osmonduu/Shooter-Controller-System/Docs/schematics/guncontroller.kicad_sch

## KiCad design Docs/schematics/guncontroller.kicad_sch (2025-05-13)

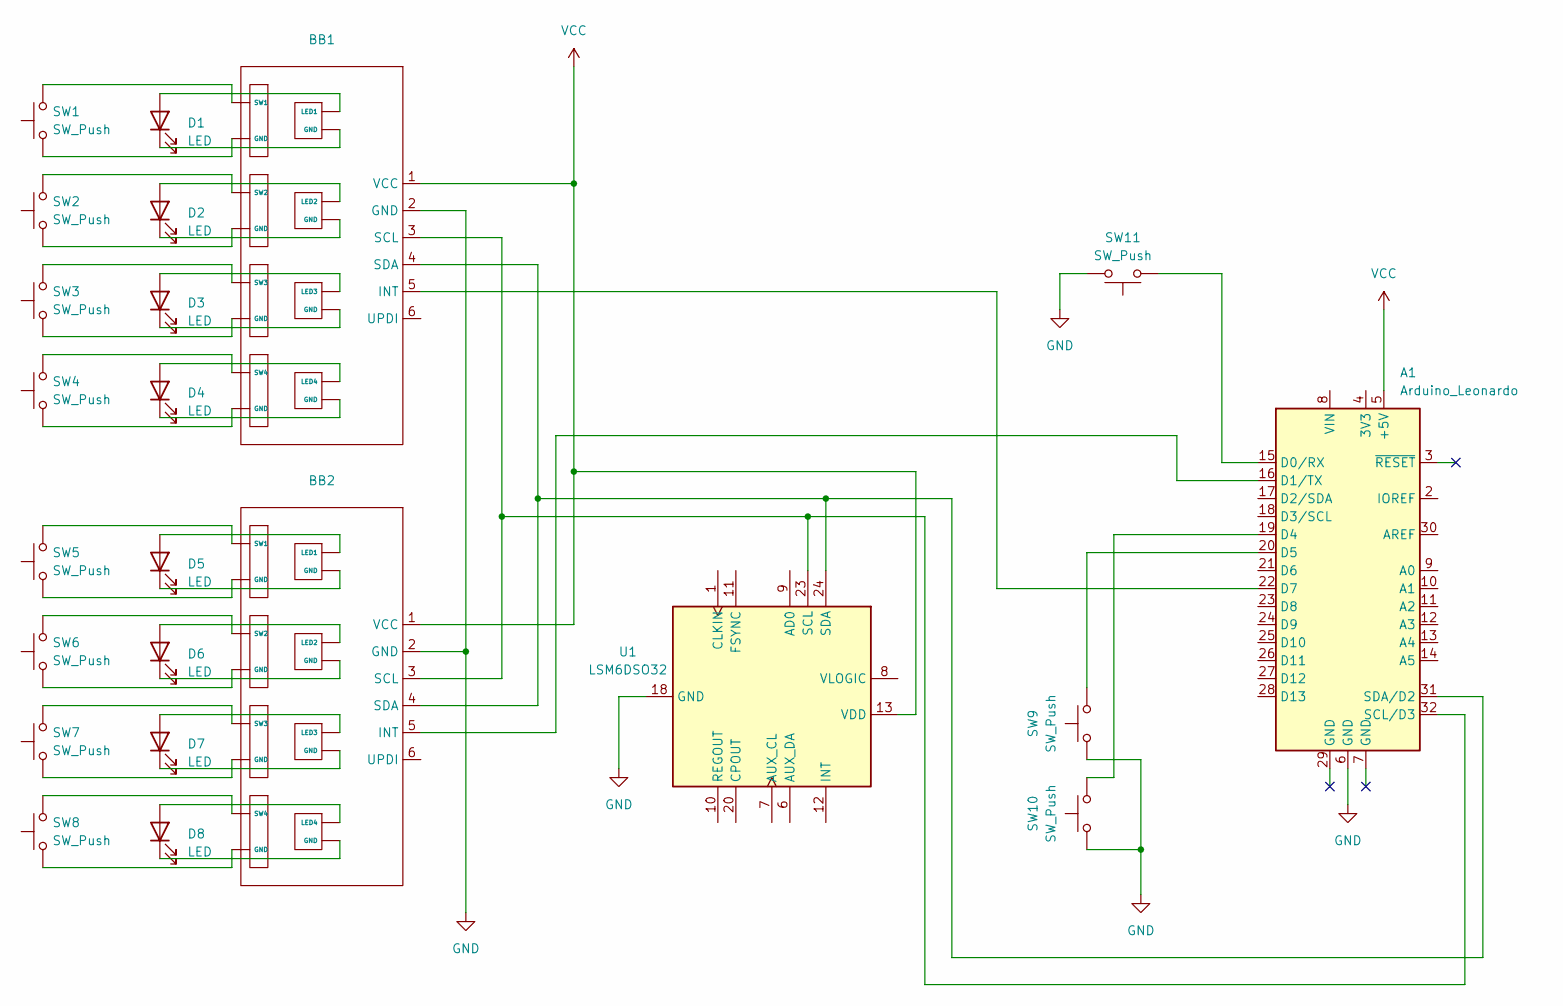
[picture p14: schematic guncontroller.kicad_sch]

Parts:
A1: Arduino_Leonardo; Arduino_UNO_R3
BB1, BB2: (no value)
D1, D2, D3, D4, D5, D6, D7, D8: LED
SW1, SW2, SW3, SW4, SW5, SW6, SW7, SW8, SW9, SW10, SW11: SW_Push
U1: LSM6DSO32; InvenSense_QFN-24_4x4mm_P0.5mm

Connections:
GND: A1.6 (GND), BB1.2 (GND), BB2.2 (GND), SW9.1, SW10.1, SW11.2, U1.18 (GND)
unnamed: A1.15 (D0/RX), SW11.1
unnamed: A1.16 (D1/TX), BB2.5 (INT)
unnamed: A1.19 (D4), SW10.2
unnamed: A1.20 (D5), SW9.2
unnamed: A1.22 (D7), BB1.5 (INT)
unnamed: A1.31 (SDA/D2), BB1.4 (SDA), BB2.4 (SDA), U1.24 (SDA)
unnamed: A1.32 (SCL/D3), BB1.3 (SCL), BB2.3 (SCL), U1.23 (SCL)
unnamed: BB1. (GND), D1.1 (K), D1.2 (A), D2.1 (K), D2.2 (A), D3.1 (K), D3.2 (A), D4.1 (K), D4.2 (A), SW1.1, SW1.2, SW2.1, SW2.2, SW3.1, SW3.2, SW4.1, SW4.2
unnamed: BB2. (GND), D5.1 (K), D5.2 (A), D6.1 (K), D6.2 (A), D7.1 (K), D7.2 (A), D8.1 (K), D8.2 (A), SW5.1, SW5.2, SW6.1, SW6.2, SW7.1, SW7.2, SW8.1, SW8.2
VCC: A1.5 (+5V), BB1.1 (VCC), BB2.1 (VCC), U1.13 (VDD)
