osmonduu/Shooter-Controller-System/Docs/schematics/movement-pad.kicad_sch

## KiCad design Docs/schematics/movement-pad.kicad_sch (2025-05-13)

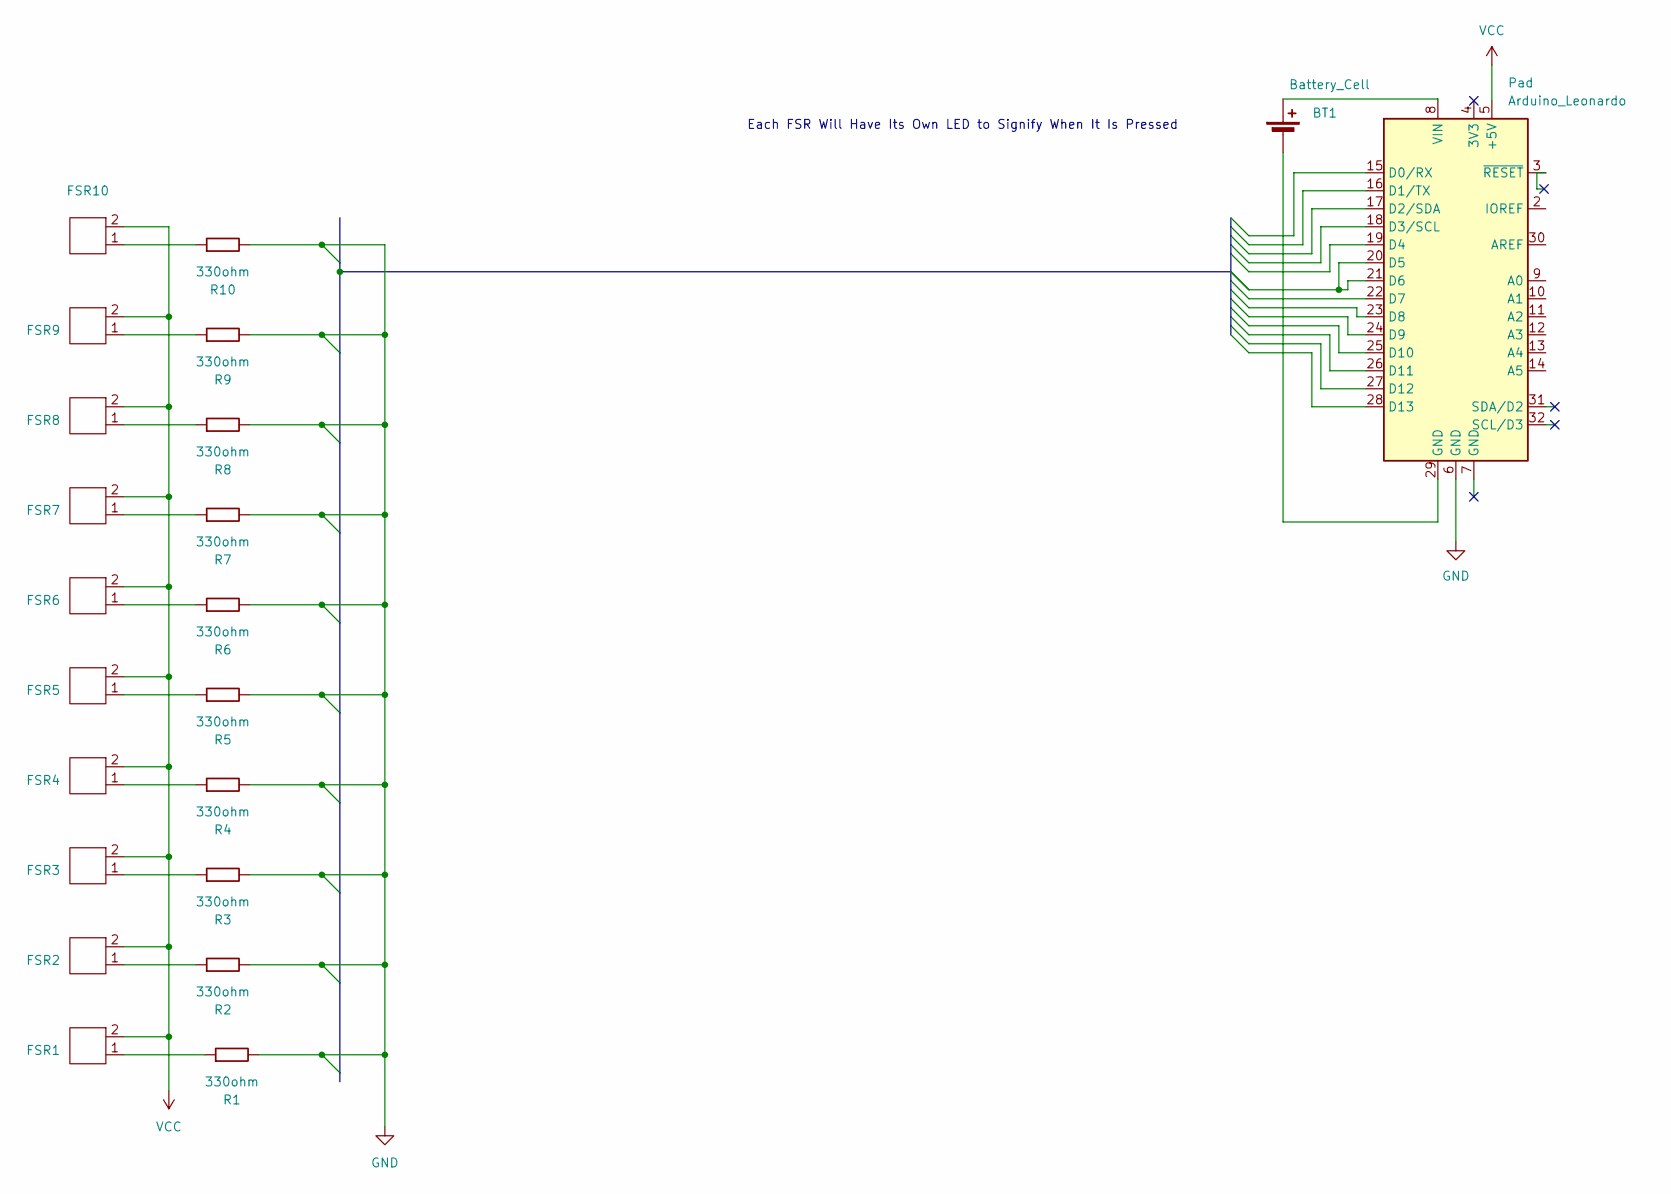
[picture p15: schematic movement-pad.kicad_sch]

Parts:
BT1: Battery_Cell
FSR1, FSR2, FSR3, FSR4, FSR5, FSR6, FSR7, FSR8, FSR9, FSR10: (no value)
Pad: Arduino_Leonardo; Arduino_UNO_R3
R1, R2, R3, R4, R5, R6, R7, R8, R9, R10: 330ohm; R_Axial_DIN0207_L6.3mm_D2.5mm_P10.16mm_Horizontal

Connections:
GND: Pad.6 (GND), R1.2, R2.2, R3.2, R4.2, R5.2, R6.2, R7.2, R8.2, R9.2, R10.2
unnamed: BT1.1 (+), Pad.8 (VIN)
unnamed: BT1.2 (-), Pad.29 (GND)
unnamed: FSR1.1, R1.1
unnamed: FSR2.1, R2.1
unnamed: FSR3.1, R3.1
unnamed: FSR4.1, R4.1
unnamed: FSR5.1, R5.1
unnamed: FSR6.1, R6.1
unnamed: FSR7.1, R7.1
unnamed: FSR8.1, R8.1
unnamed: FSR9.1, R9.1
unnamed: FSR10.1, R10.1
unnamed: Pad.20 (D5), Pad.21 (D6)
VCC: FSR1.2, FSR2.2, FSR3.2, FSR4.2, FSR5.2, FSR6.2, FSR7.2, FSR8.2, FSR9.2, FSR10.2, Pad.5 (+5V)

Notes on the sheet:
Each FSR Will Have Its Own LED to Signify When It Is Pressed
